fabPlane/gb-devcart/3dmodels/SOT-23-6.step

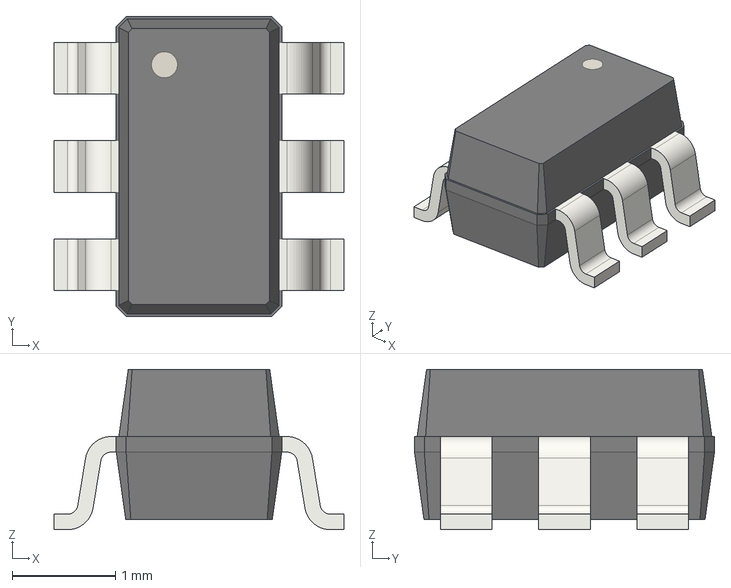
[picture p27: CAD file, 2026-10-02]
3dmodels/SOT-23-6.step
2.80 x 2.90 x 1.55 mm
