fabPlane/gb-devcart/3dmodels/TSOP-I-48_18.4x12mm_P0.5mm.step

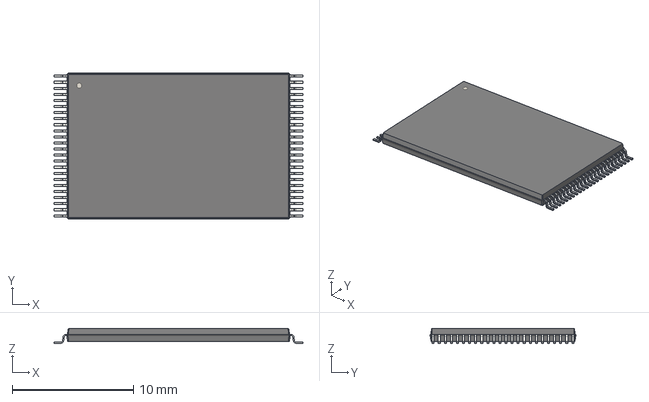
[picture p28: CAD file, 2026-10-02]
3dmodels/TSOP-I-48_18.4x12mm_P0.5mm.step
20.5 x 12.0 x 1.20 mm
