fabPlane/gb-devcart/3dmodels/SOT-23.step

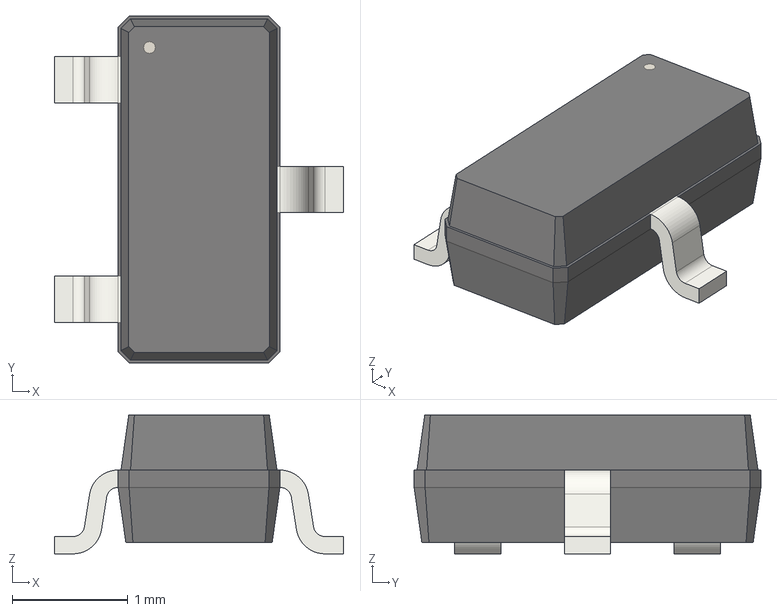
[picture p29: CAD file, 2026-10-02]
3dmodels/SOT-23.step
2.50 x 3.00 x 1.20 mm
