fabPlane/gb-devcart/3dmodels/QFN-28-1EP_4x4mm_P0.4mm_EP2.4x2.4mm.step

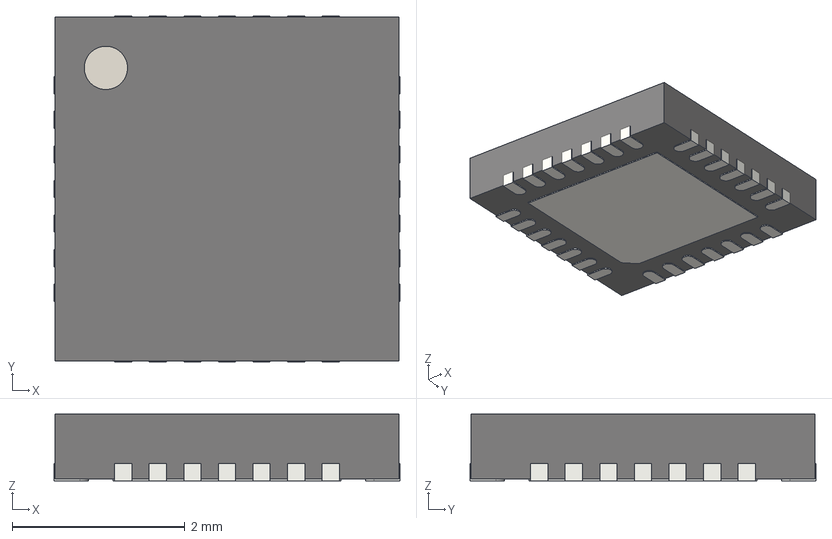
[picture p30: CAD file, 2026-10-02]
3dmodels/QFN-28-1EP_4x4mm_P0.4mm_EP2.4x2.4mm.step
4.00 x 4.00 x 0.77 mm
