fabPlane/gb-devcart/3dmodels/SOIC-28W_7.5x17.9mm_P1.27mm.step

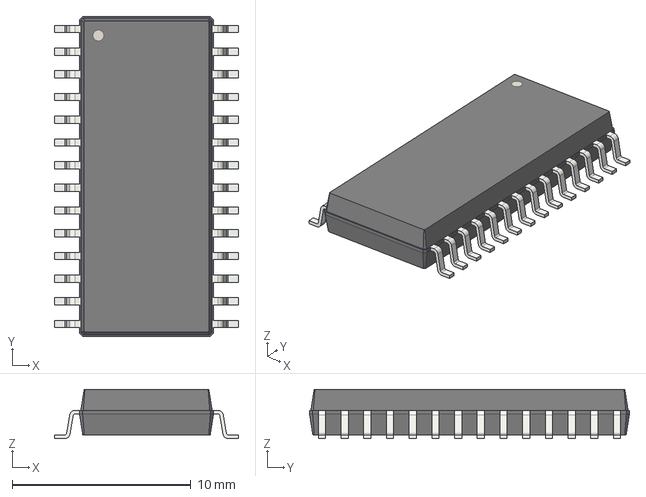
[picture p31: CAD file, 2026-10-01]
3dmodels/SOIC-28W_7.5x17.9mm_P1.27mm.step
10.3 x 17.9 x 2.75 mm
