fabPlane/gb-devcart/3dmodels/SOIC-14_3.9x8.7mm_P1.27mm.step

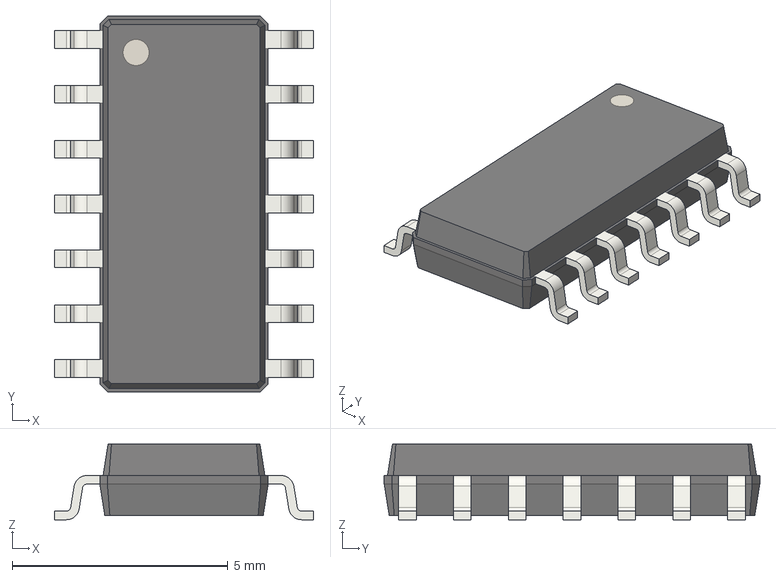
[picture p32: CAD file, 2026-10-01]
3dmodels/SOIC-14_3.9x8.7mm_P1.27mm.step
6.00 x 8.70 x 1.75 mm
