fabPlane/gb-devcart/3dmodels/R_0603_1608Metric.step

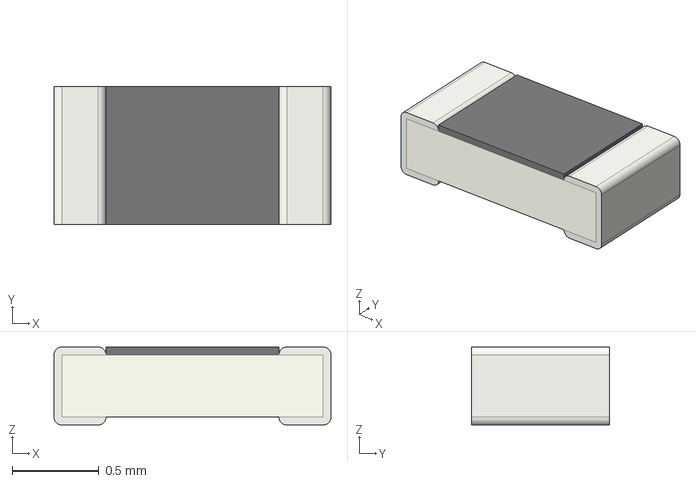
[picture p33: CAD file, 2026-10-01]
3dmodels/R_0603_1608Metric.step
1.60 x 0.8 x 0.45 mm
