fabPlane/gb-devcart/3dmodels/PLCC-32_11.4x14.0mm_P1.27mm.step

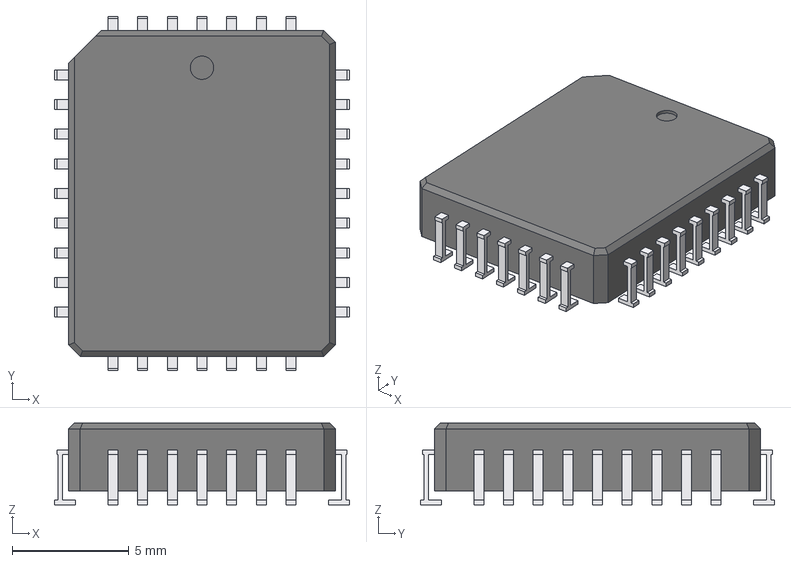
[picture p34: CAD file, 2026-10-01]
3dmodels/PLCC-32_11.4x14.0mm_P1.27mm.step
12.6 x 15.2 x 3.50 mm
leads
