fabPlane/gb-devcart/3dmodels/SOIC-20W_7.5x12.8mm_P1.27mm.step

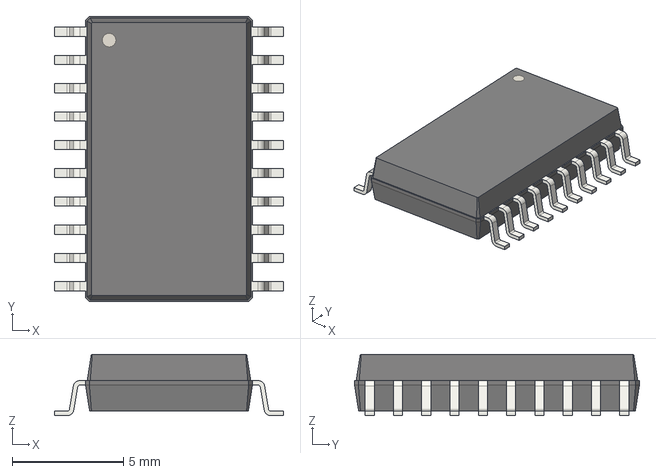
[picture p35: CAD file, 2026-10-01]
3dmodels/SOIC-20W_7.5x12.8mm_P1.27mm.step
10.3 x 12.8 x 2.75 mm
