fabPlane/gb-devcart/3dmodels/C_0603_1608Metric.step

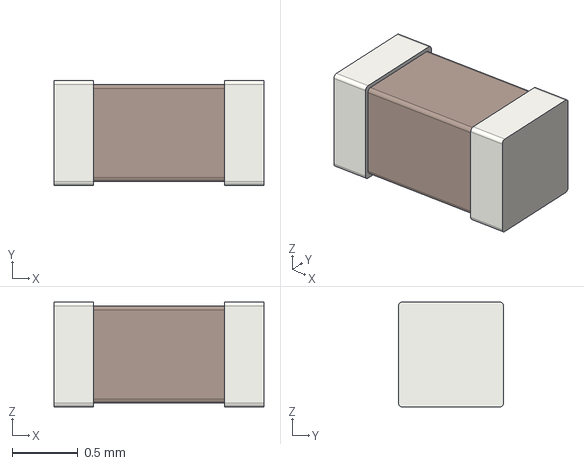
[picture p36: CAD file, 2026-10-01]
3dmodels/C_0603_1608Metric.step
1.60 x 0.8 x 0.8 mm
