fabPlane/gb-devcart/3dmodels/C_1206_3216Metric.step

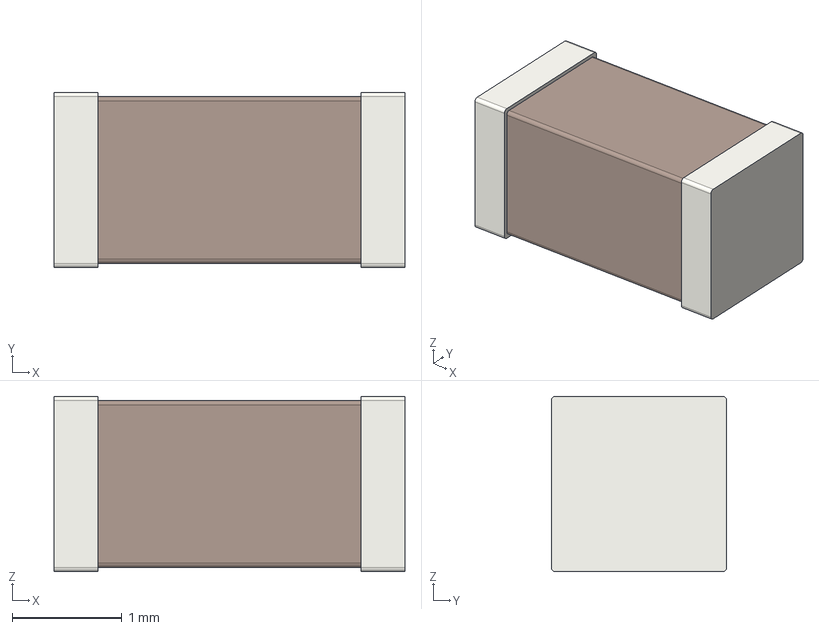
[picture p37: CAD file, 2026-10-01]
3dmodels/C_1206_3216Metric.step
3.20 x 1.60 x 1.60 mm
